MarvinHill/3d-scanner/3d/camholder1.stl

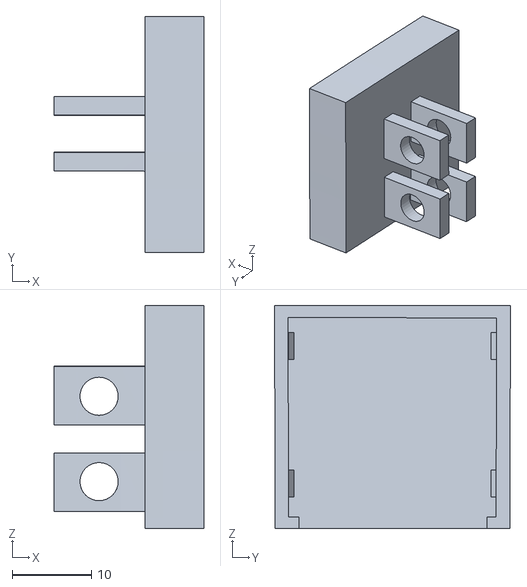
[picture p15: CAD file, 2024-08-01]
3d/camholder1.stl
18.8 x 29.7 x 28.1
