MarvinHill/3d-scanner/3d/gear1.stl

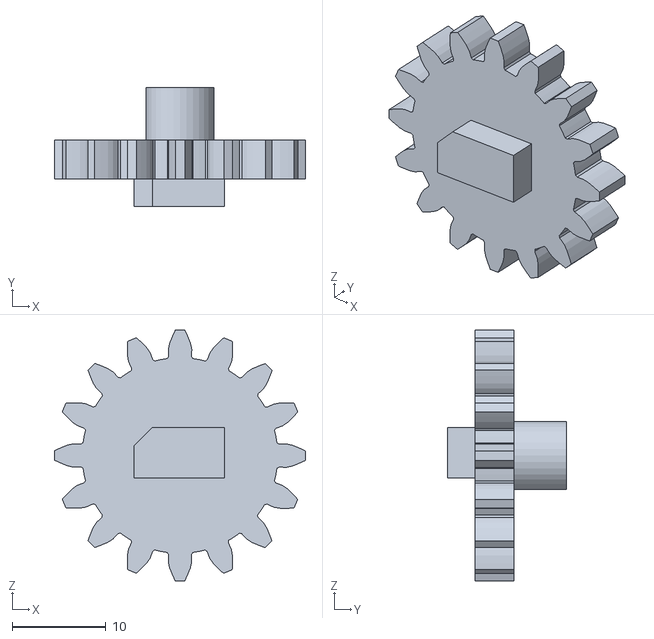
[picture p16: CAD file, 2024-08-01]
3d/gear1.stl
26.8 x 12.7 x 26.8
