MarvinHill/3d-scanner/3d/table.stl

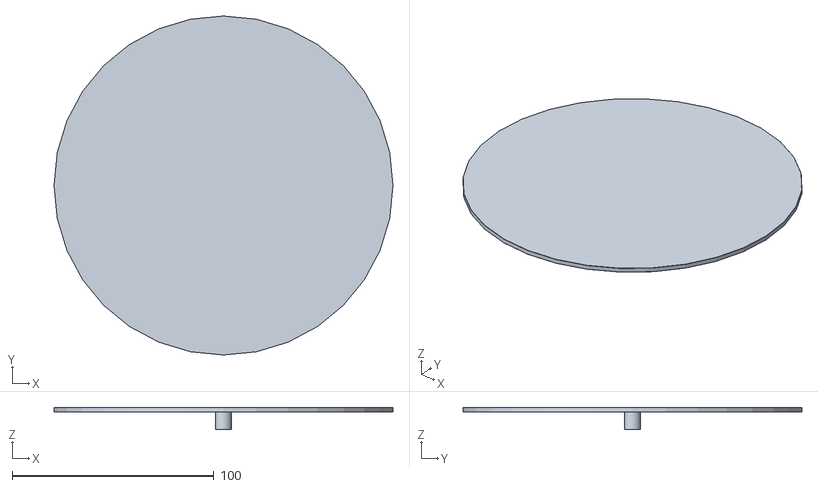
[picture p17: CAD file, 2024-08-01]
3d/table.stl
168.0 x 168.0 x 11.0
