MarvinHill/3d-scanner/3d/stabplate.stl

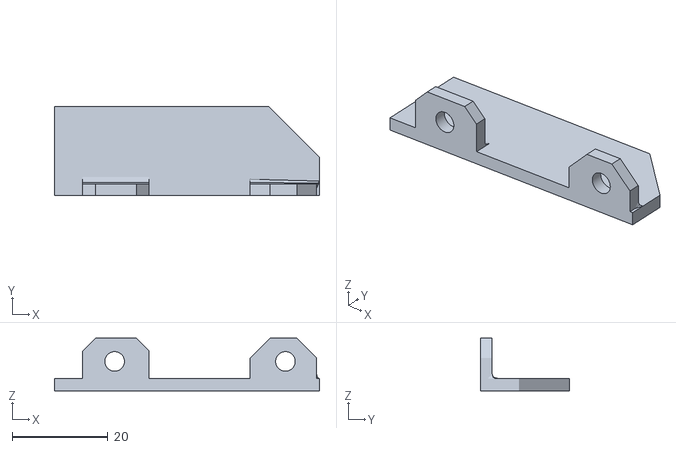
[picture p18: CAD file, 2024-08-01]
3d/stabplate.stl
55.3 x 18.6 x 11.0
