MarvinHill/3d-scanner/3d/motordriver1.stl

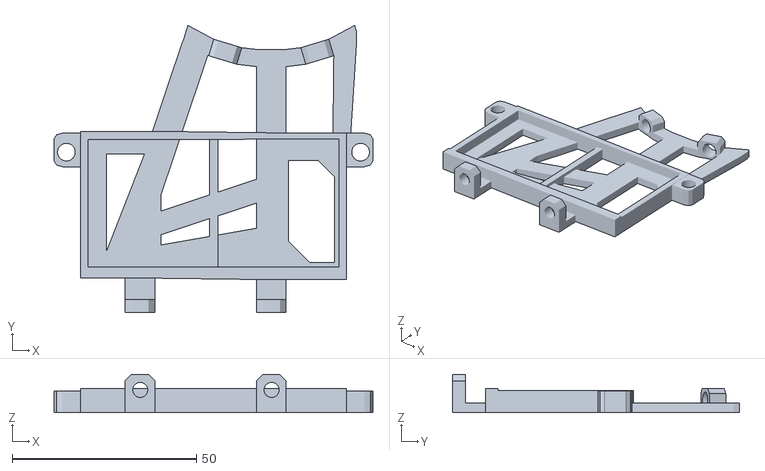
[picture p19: CAD file, 2024-08-01]
3d/motordriver1.stl
86.6 x 78.0 x 10.4
