MarvinHill/3d-scanner/3d/adjustablearm.stl

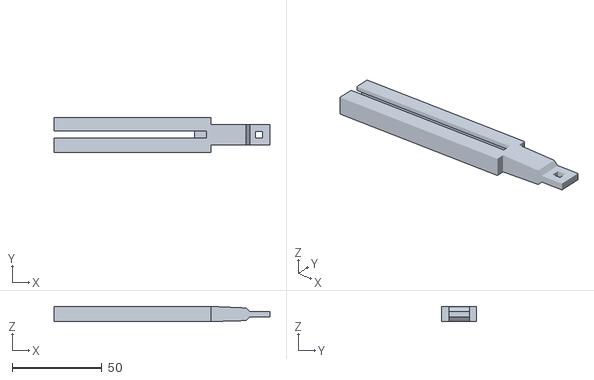
[picture p20: CAD file, 2024-08-01]
3d/adjustablearm.stl
120.3 x 19.3 x 8.45
